JOYFanShu/FanShu-MSc-Advanced-Project/Physical model/2D053D68-A871-4A51-8CC4-EDA1FF286877-5026-000003B99A61D872.JPG

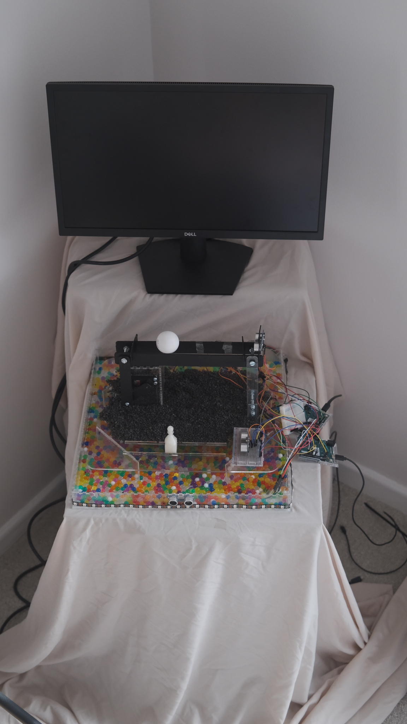
Physical model/2D053D68-A871-4A51-8CC4-EDA1FF286877-5026-000003B99A61D872.JPG
