JOYFanShu/FanShu-MSc-Advanced-Project/Physical model/8123582E-3AA2-40D9-810A-F3E6E53FE559-5026-000003B9BA3C1011.JPG

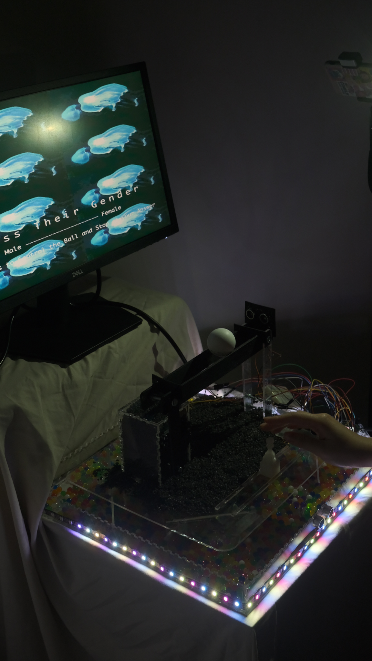
Physical model/8123582E-3AA2-40D9-810A-F3E6E53FE559-5026-000003B9BA3C1011.JPG
