JOYFanShu/FanShu-MSc-Advanced-Project/Physical model/A68C4EFC-19B7-4E6E-B147-6552091602A3-5026-000003B9B2F27EF1.JPG

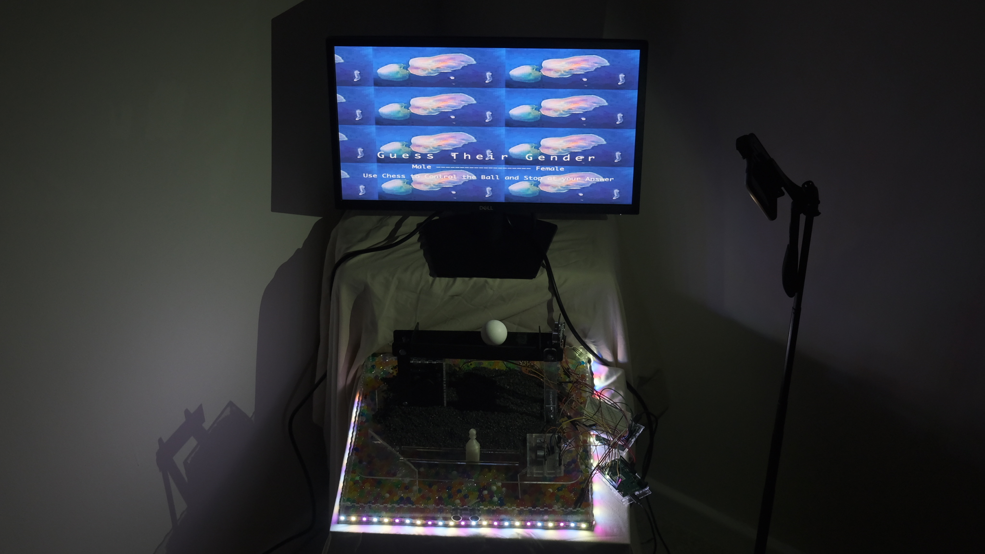
Physical model/A68C4EFC-19B7-4E6E-B147-6552091602A3-5026-000003B9B2F27EF1.JPG
