JOYFanShu/FanShu-MSc-Advanced-Project/TouchDesigner/01.png

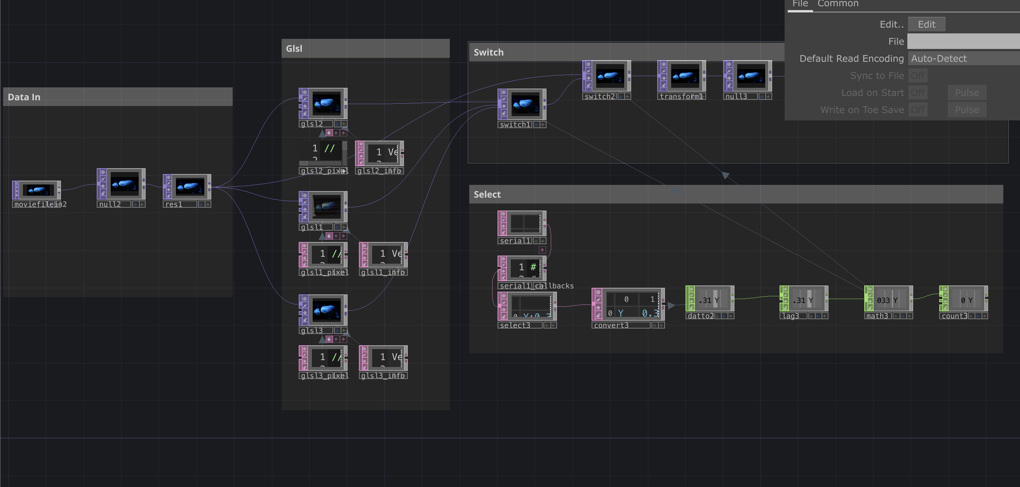
TouchDesigner/01.png
