JOYFanShu/FanShu-MSc-Advanced-Project/TouchDesigner/02.png

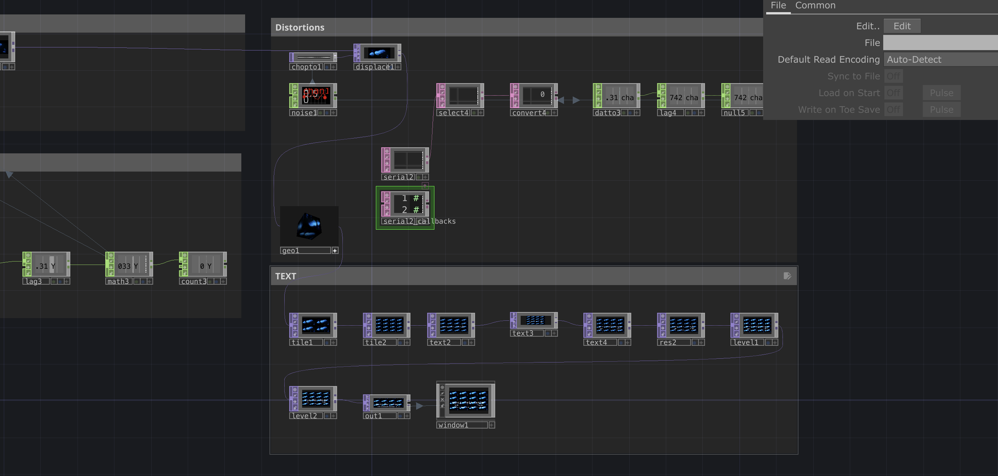
TouchDesigner/02.png
