JOYFanShu/FanShu-MSc-Advanced-Project/TouchDesigner/05.png

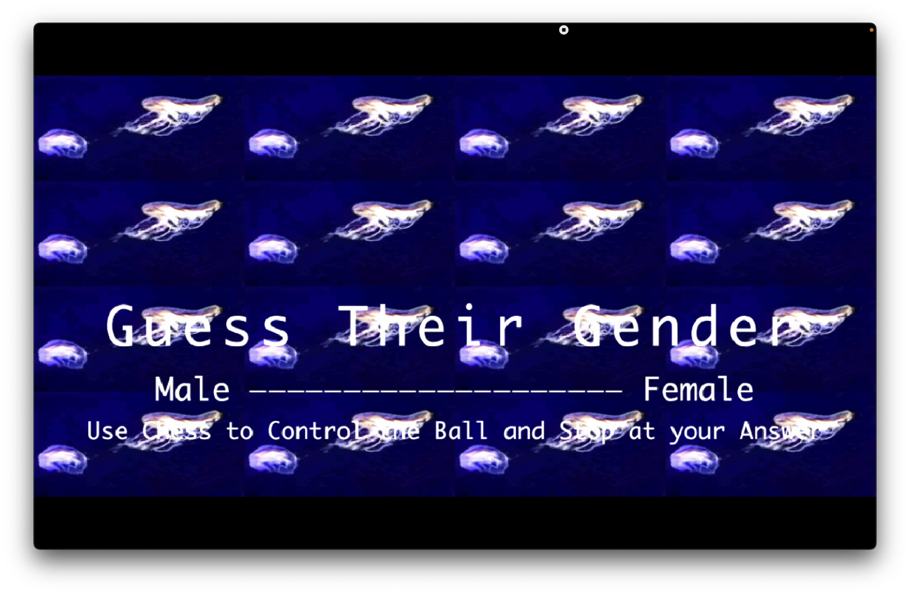
TouchDesigner/05.png
