JOYFanShu/FanShu-MSc-Advanced-Project/Video-Machine Learning/picture/jellyfish1.png

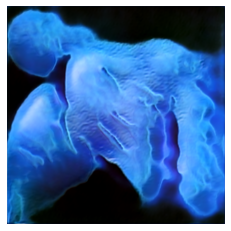
Video-Machine Learning/picture/jellyfish1.png
