JOYFanShu/FanShu-MSc-Advanced-Project/Video-Machine Learning/picture/jellyfish2.png

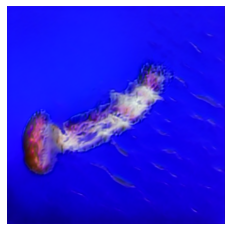
Video-Machine Learning/picture/jellyfish2.png
