JOYFanShu/FanShu-MSc-Advanced-Project/Video-Machine Learning/picture/jellyfish3.png

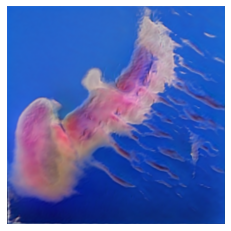
Video-Machine Learning/picture/jellyfish3.png
