JOYFanShu/FanShu-MSc-Advanced-Project/Video-Machine Learning/picture/jellyfish4.png

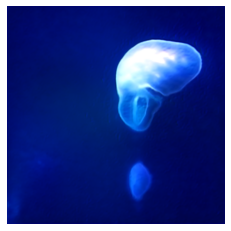
Video-Machine Learning/picture/jellyfish4.png
