JOYFanShu/FanShu-MSc-Advanced-Project/Video-Machine Learning/picture/jellyfish5.png

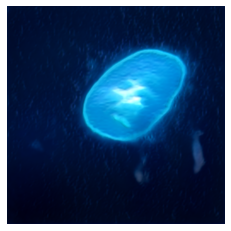
Video-Machine Learning/picture/jellyfish5.png
