JOYFanShu/FanShu-MSc-Advanced-Project/Video-Machine Learning/picture/jellyfish6.png

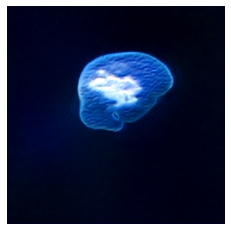
Video-Machine Learning/picture/jellyfish6.png
