JOYFanShu/FanShu-MSc-Advanced-Project/Video-Machine Learning/picture/jellyfish7.png

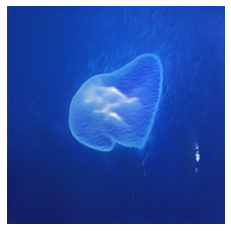
Video-Machine Learning/picture/jellyfish7.png
