JOYFanShu/FanShu-MSc-Advanced-Project/Video-Machine Learning/picture/jellyfish9.png

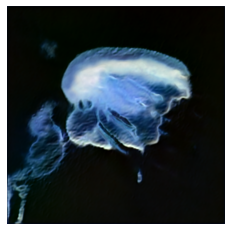
Video-Machine Learning/picture/jellyfish9.png
