JOYFanShu/FanShu-MSc-Advanced-Project/Video-Machine Learning/picture/jellyfish10.png

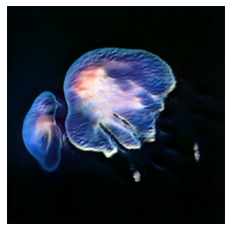
Video-Machine Learning/picture/jellyfish10.png
