JOYFanShu/FanShu-MSc-Advanced-Project/Video-Machine Learning/picture/jellyfish11.png

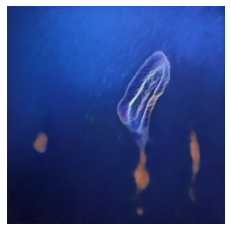
Video-Machine Learning/picture/jellyfish11.png
