JOYFanShu/FanShu-MSc-Advanced-Project/Video-Machine Learning/picture/jellyfish12.png

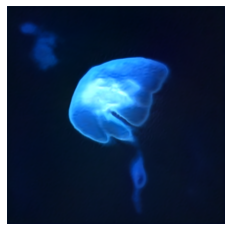
Video-Machine Learning/picture/jellyfish12.png
