JOYFanShu/FanShu-MSc-Advanced-Project/Video-Machine Learning/picture/jellyfish13.png

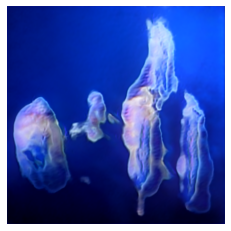
Video-Machine Learning/picture/jellyfish13.png
