JOYFanShu/FanShu-MSc-Advanced-Project/Video-Machine Learning/picture/jellyfish14.png

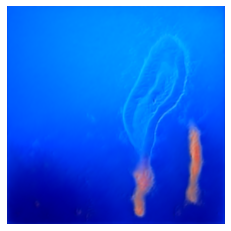
Video-Machine Learning/picture/jellyfish14.png
