JOYFanShu/FanShu-MSc-Advanced-Project/Video-Machine Learning/picture/jellyfish15.png

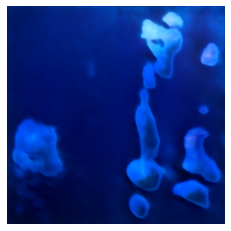
Video-Machine Learning/picture/jellyfish15.png
