JOYFanShu/FanShu-MSc-Advanced-Project/Video-Machine Learning/picture/jellyfish16.png

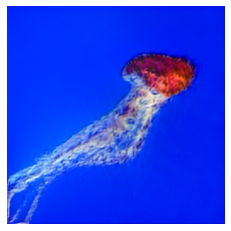
Video-Machine Learning/picture/jellyfish16.png
