JOYFanShu/FanShu-MSc-Advanced-Project/Video-Machine Learning/picture/jellyfish17.png

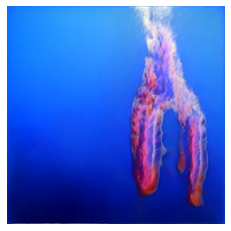
Video-Machine Learning/picture/jellyfish17.png
