JOYFanShu/FanShu-MSc-Advanced-Project/Video-Machine Learning/picture/jellyfish19.png

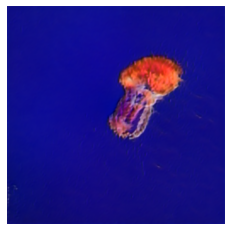
Video-Machine Learning/picture/jellyfish19.png
