JOYFanShu/FanShu-MSc-Advanced-Project/Video-Machine Learning/picture/jellyfish21.png

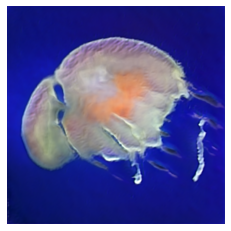
Video-Machine Learning/picture/jellyfish21.png
