JOYFanShu/FanShu-MSc-Advanced-Project/Video-Machine Learning/picture/jellyfish24.png

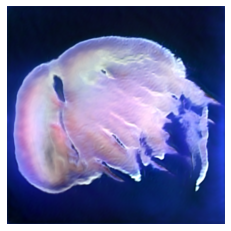
Video-Machine Learning/picture/jellyfish24.png
