JOYFanShu/FanShu-MSc-Advanced-Project/Video-Machine Learning/picture/jellyfish25.png

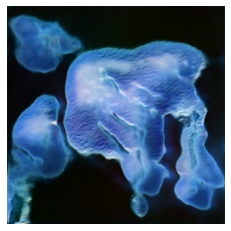
Video-Machine Learning/picture/jellyfish25.png
