JOYFanShu/FanShu-MSc-Advanced-Project/Video-Machine Learning/picture/jellyfish26.png

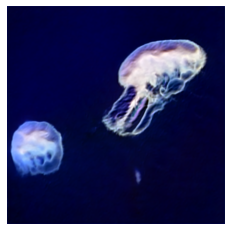
Video-Machine Learning/picture/jellyfish26.png
