JOYFanShu/FanShu-MSc-Advanced-Project/Video-Machine Learning/picture/jellyfish27.png

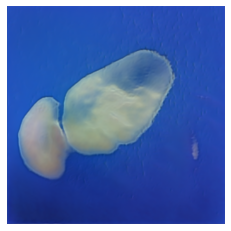
Video-Machine Learning/picture/jellyfish27.png
